OLIMEX/S3-OLinuXino/HARDWARE/S3-OLinuXino-Rev_A-preliminary/images/img3.png

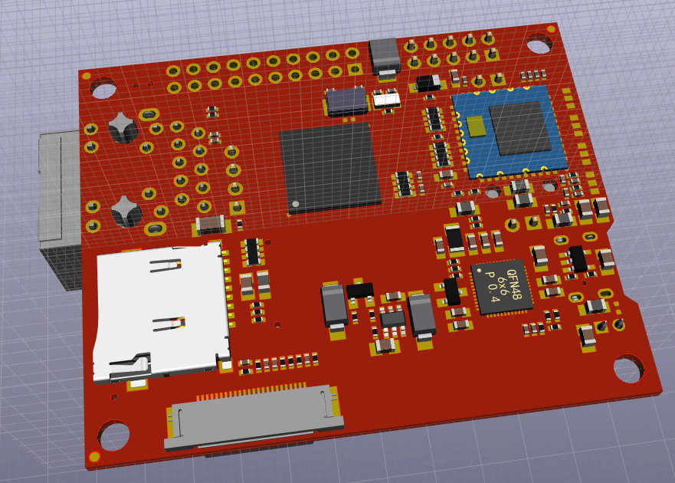
HARDWARE/S3-OLinuXino-Rev_A-preliminary/images/img3.png
