OLIMEX/S3-OLinuXino/HARDWARE/S3-OLinuXino-Rev_A-preliminary/3d/FPV-WZA21-40-LF_Molex-541044033.stp

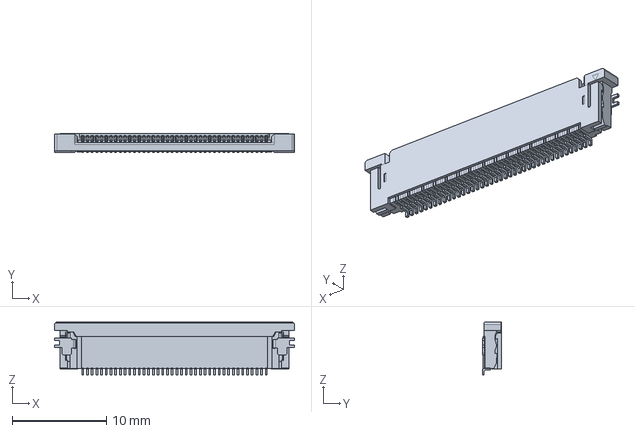
[picture p15: CAD file, 2020-04-24]
HARDWARE/S3-OLinuXino-Rev_A-preliminary/3d/FPV-WZA21-40-LF_Molex-541044033.stp
25.5 x 2.05 x 5.60 mm
