OLIMEX/S3-OLinuXino/HARDWARE/S3-OLinuXino_Rev_A-release/3d/SOT-23.step

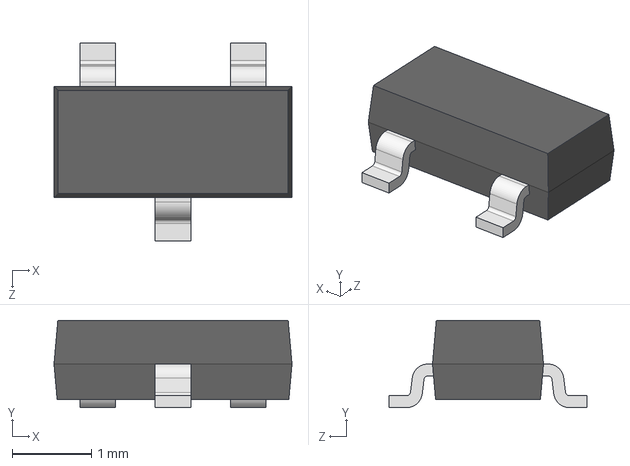
[picture p16: CAD file, 2020-04-24]
HARDWARE/S3-OLinuXino_Rev_A-release/3d/SOT-23.step
3.00 x 1.10 x 2.50 mm
