OLIMEX/S3-OLinuXino/HARDWARE/S3-OLinuXino-Rev_A-preliminary/3d/L-CD32_shielded.step

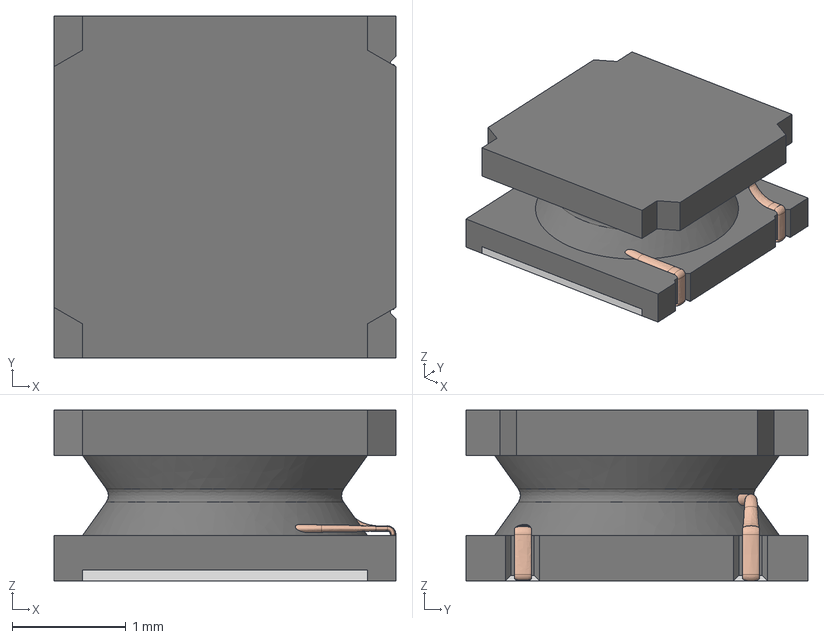
[picture p17: CAD file, 2020-04-24]
HARDWARE/S3-OLinuXino-Rev_A-preliminary/3d/L-CD32_shielded.step
3.00 x 3.00 x 1.50 mm
