OLIMEX/S3-OLinuXino/HARDWARE/S3-OLinuXino-Rev_A-preliminary/3d/TE_Connectivity-RJ45_JACK_MAG._POE_1GB_LED_1X1(2337992-8).stp

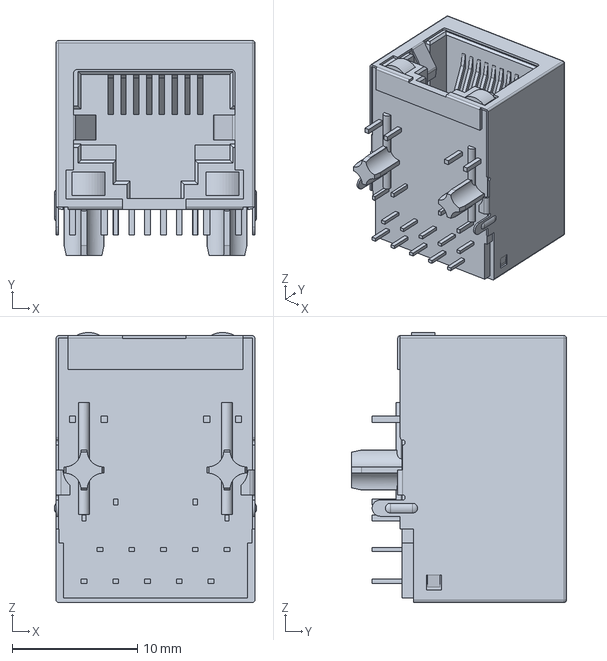
[picture p18: CAD file, 2020-04-24]
HARDWARE/S3-OLinuXino-Rev_A-preliminary/3d/TE_Connectivity-RJ45_JACK_MAG._POE_1GB_LED_1X1(2337992-8).stp
16.2 x 17.2 x 21.6 mm
