OLIMEX/S3-OLinuXino/HARDWARE/S3-OLinuXino_Rev_A-release/3d/it1185.step

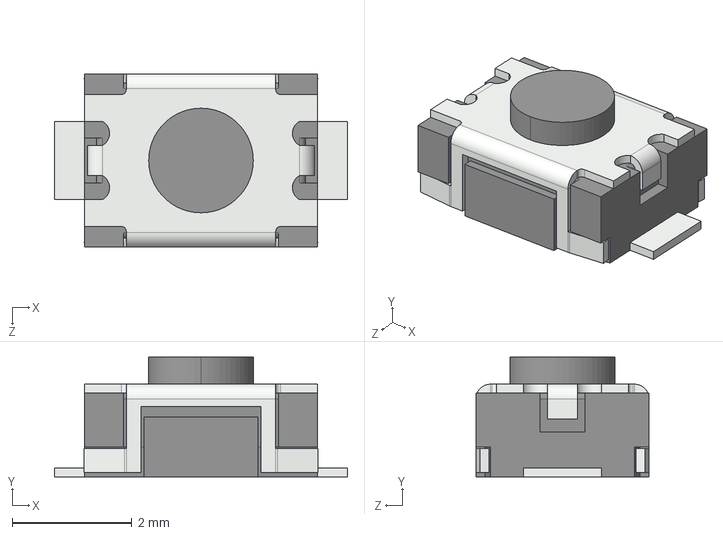
[picture p19: CAD file, 2020-04-24]
HARDWARE/S3-OLinuXino_Rev_A-release/3d/it1185.step
4.90 x 2.00 x 2.90 mm
