OLIMEX/S3-OLinuXino/HARDWARE/S3-OLinuXino_Rev_A-release/3d/RaspberryPiLCD-MiPi_Connector-TE_1-1734248-5.stp

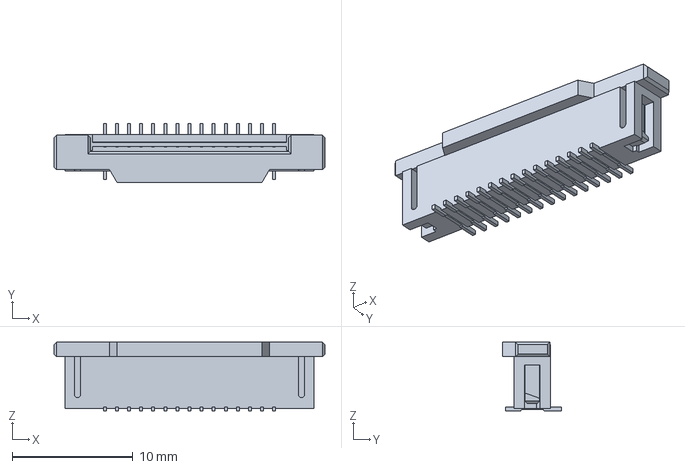
[picture p20: CAD file, 2020-04-24]
HARDWARE/S3-OLinuXino_Rev_A-release/3d/RaspberryPiLCD-MiPi_Connector-TE_1-1734248-5.stp
22.4 x 4.85 x 5.68 mm
