OLIMEX/S3-OLinuXino/HARDWARE/S3-OLinuXino-Rev_A-preliminary/3d/CUI_SJ-43515TS-SMT-TR.step

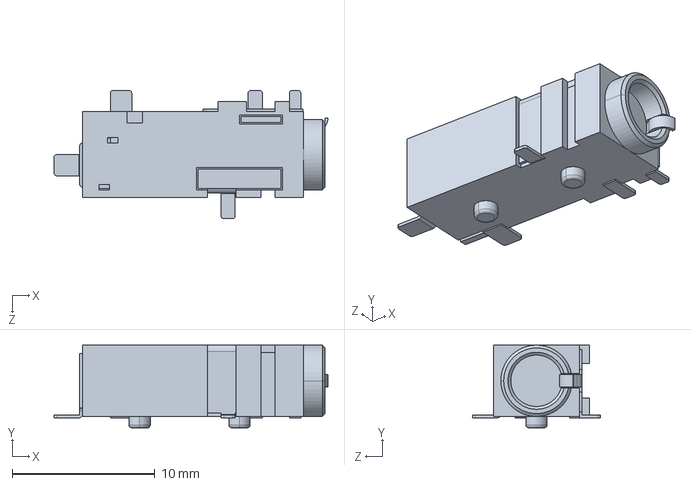
[picture p21: CAD file, 2020-04-24]
HARDWARE/S3-OLinuXino-Rev_A-preliminary/3d/CUI_SJ-43515TS-SMT-TR.step
19.2 x 5.80 x 9.00 mm
