OLIMEX/S3-OLinuXino/HARDWARE/S3-OLinuXino_Rev_A-release/3d/QSG5032.step

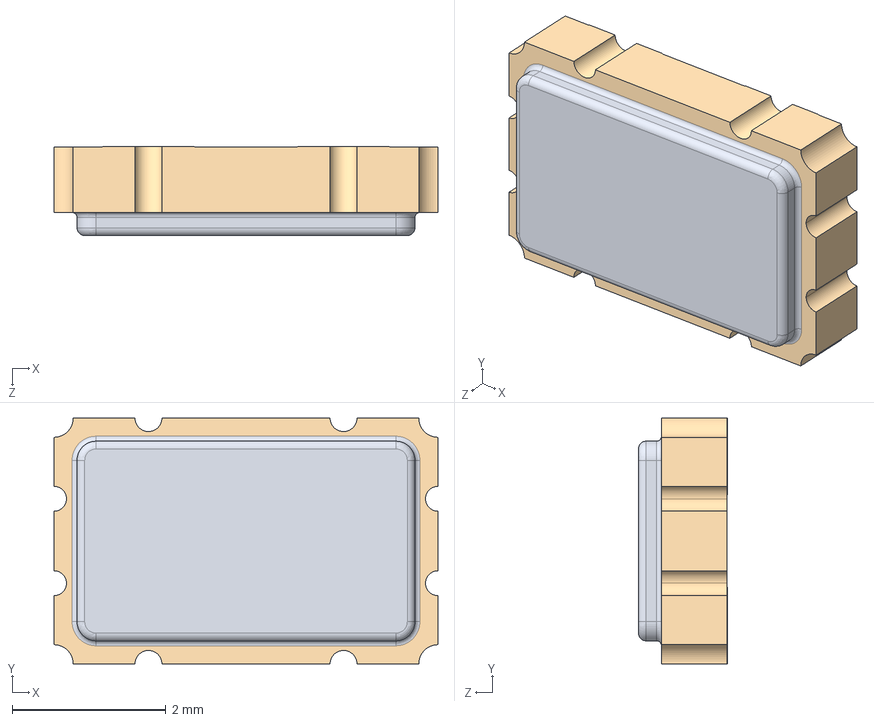
[picture p22: CAD file, 2020-04-24]
HARDWARE/S3-OLinuXino_Rev_A-release/3d/QSG5032.step
5.00 x 3.20 x 1.16 mm
