OLIMEX/S3-OLinuXino/HARDWARE/S3-OLinuXino-Rev_A-preliminary/3d/BGA-256_11.0x11.0mm_Layout20x20_P0.5mm_Ball0.3mm_Pad0.25mm_NSMD.step

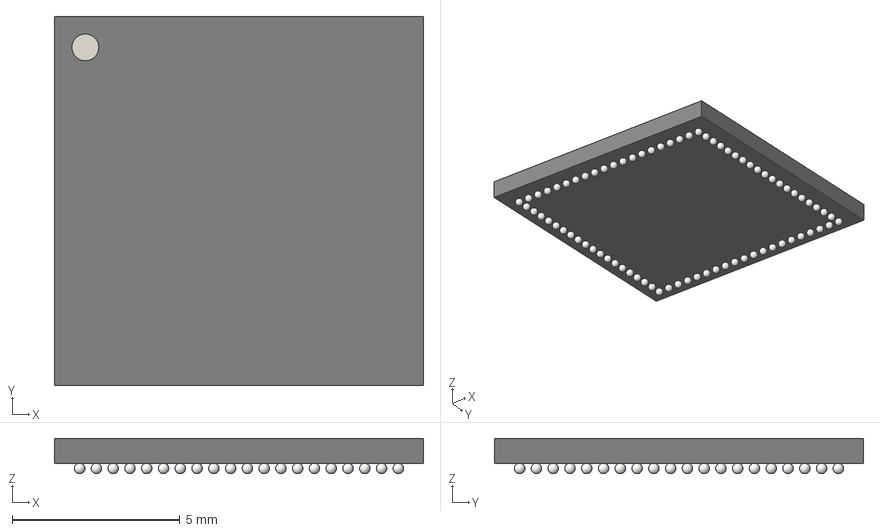
[picture p23: CAD file, 2020-04-24]
HARDWARE/S3-OLinuXino-Rev_A-preliminary/3d/BGA-256_11.0x11.0mm_Layout20x20_P0.5mm_Ball0.3mm_Pad0.25mm_NSMD.step
11.0 x 11.0 x 1.06 mm
