OLIMEX/S3-OLinuXino/HARDWARE/S3-OLinuXino_Rev_A-release/3d/SO-8_150mil---SN65HVDA1050AQDRQ1.STEP

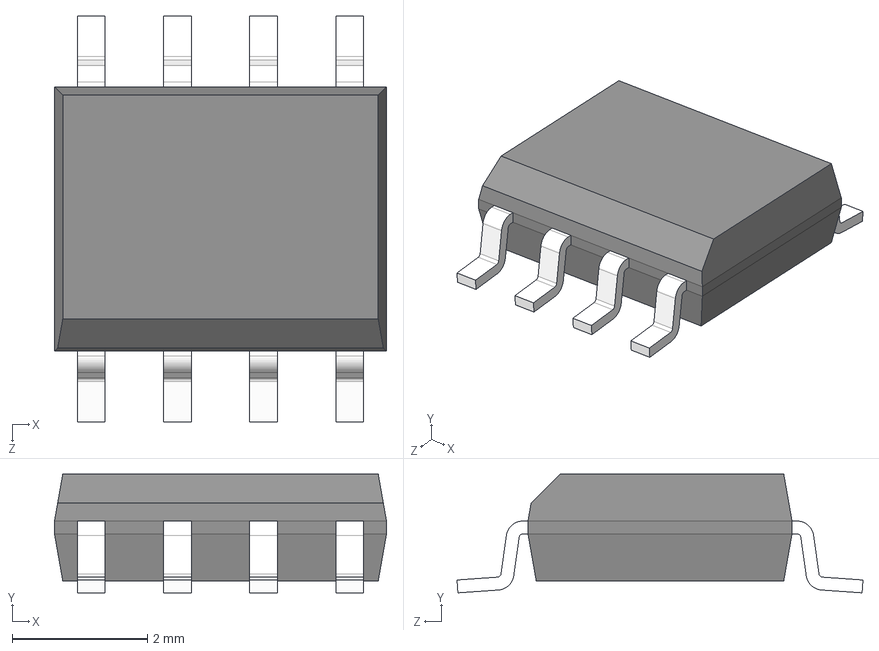
[picture p24: CAD file, 2020-04-24]
HARDWARE/S3-OLinuXino_Rev_A-release/3d/SO-8_150mil---SN65HVDA1050AQDRQ1.STEP
4.90 x 1.75 x 5.99 mm
