OLIMEX/S3-OLinuXino/HARDWARE/S3-OLinuXino-Rev_A-preliminary/3d/QFN-48_6x6mm_Pitch-0.4mm.STEP

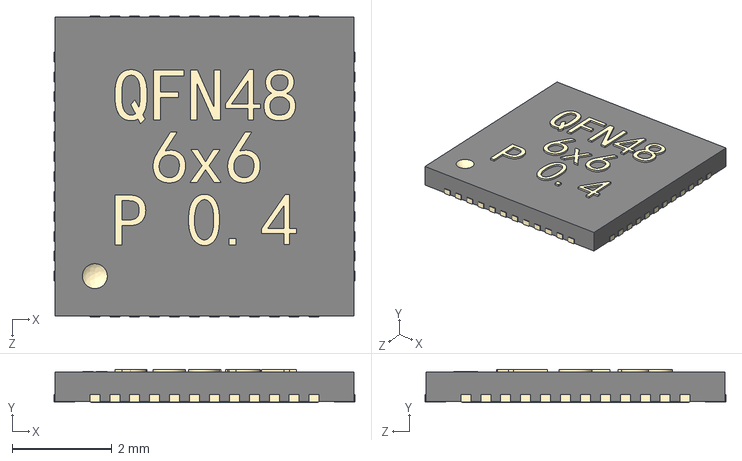
[picture p25: CAD file, 2020-04-24]
HARDWARE/S3-OLinuXino-Rev_A-preliminary/3d/QFN-48_6x6mm_Pitch-0.4mm.STEP
6.04 x 0.67 x 6.04 mm
