OLIMEX/S3-OLinuXino/HARDWARE/S3-OLinuXino_Rev_A-release/3d/L-CD75(YS75)_7.80x7.00x5.50mm.step

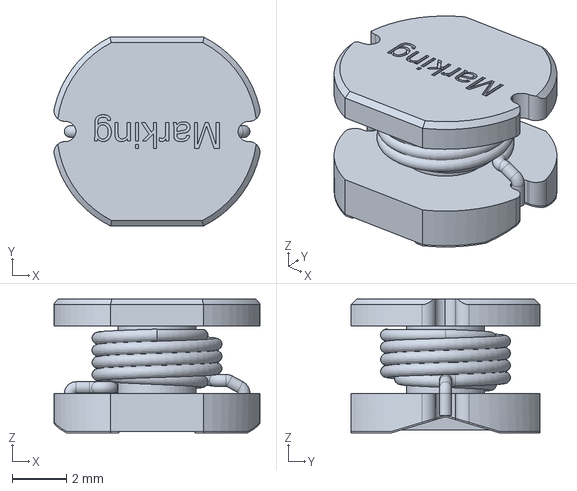
[picture p26: CAD file, 2020-04-24]
HARDWARE/S3-OLinuXino_Rev_A-release/3d/L-CD75(YS75)_7.80x7.00x5.50mm.step
7.63 x 7.00 x 4.95 mm
