OLIMEX/S3-OLinuXino/HARDWARE/S3-OLinuXino_Rev_A-release/3d/20PinMaleSmt.stp

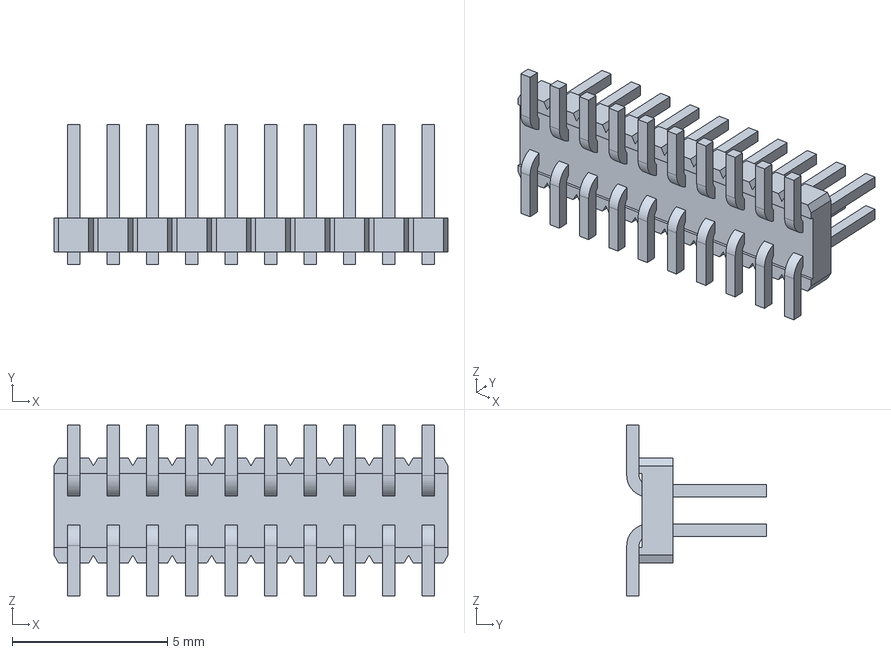
[picture p27: CAD file, 2020-04-24]
HARDWARE/S3-OLinuXino_Rev_A-release/3d/20PinMaleSmt.stp
12.7 x 4.50 x 5.50 mm
