OLIMEX/S3-OLinuXino/HARDWARE/S3-OLinuXino-Rev_A-preliminary/3d/SMD5032.STEP

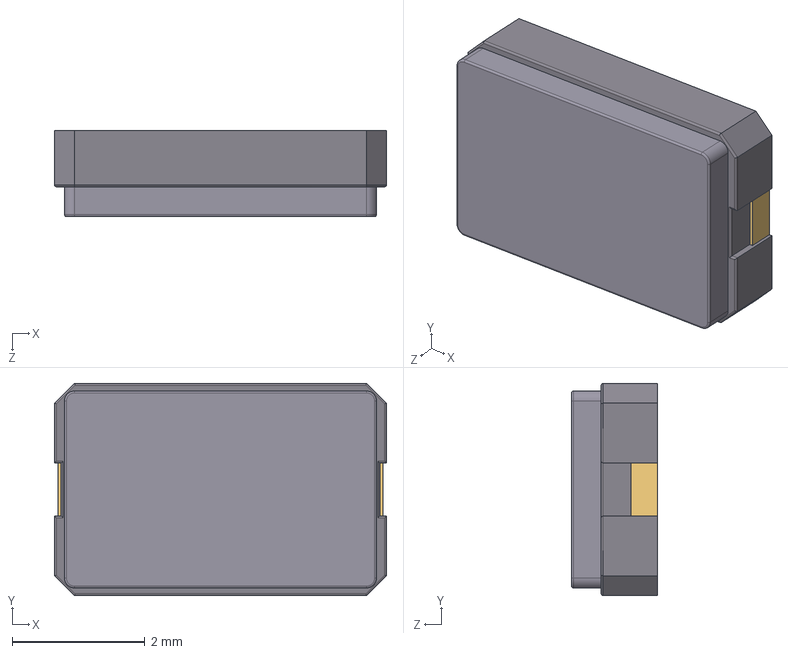
[picture p28: CAD file, 2020-04-24]
HARDWARE/S3-OLinuXino-Rev_A-preliminary/3d/SMD5032.STEP
5.00 x 3.20 x 1.30 mm
User Library-ABM3-1_Fillet002
User Library-ABM3-1_Fillet001
User Library-ABM3-1_Pad001
