OLIMEX/S3-OLinuXino/HARDWARE/S3-OLinuXino-Rev_A-preliminary/3d/HN1x2-PinHeader_1x02_P2.54mm_Vertical.step

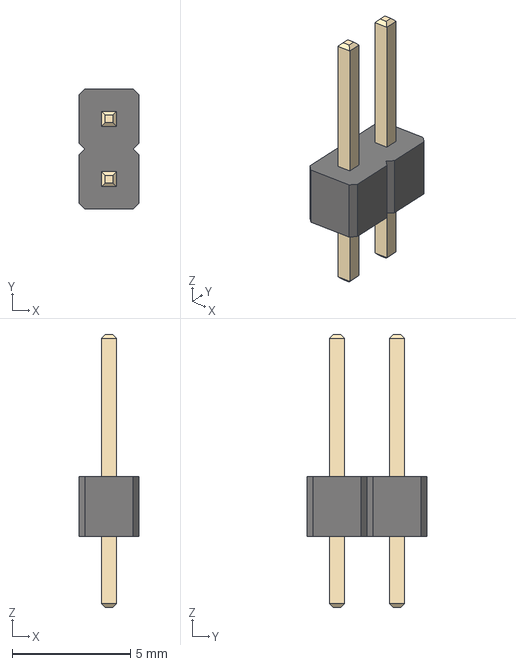
[picture p29: CAD file, 2019-10-25]
HARDWARE/S3-OLinuXino-Rev_A-preliminary/3d/HN1x2-PinHeader_1x02_P2.54mm_Vertical.step
2.54 x 5.08 x 11.5 mm
