OLIMEX/S3-OLinuXino/HARDWARE/S3-OLinuXino_Rev_A-release/3d/HN1x4-PinHeader_1x04_P2.54mm_Vertical.step

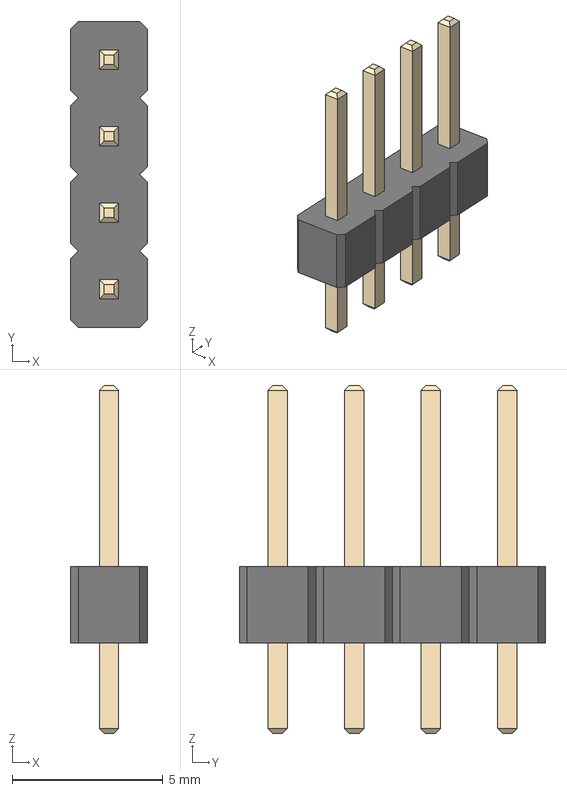
[picture p30: CAD file, 2019-10-25]
HARDWARE/S3-OLinuXino_Rev_A-release/3d/HN1x4-PinHeader_1x04_P2.54mm_Vertical.step
2.54 x 10.2 x 11.5 mm
