OLIMEX/S3-OLinuXino/HARDWARE/S3-OLinuXino-Rev_A-preliminary/3d/HN2x5-PinHeader_2x05_P2.54mm_Vertical.step

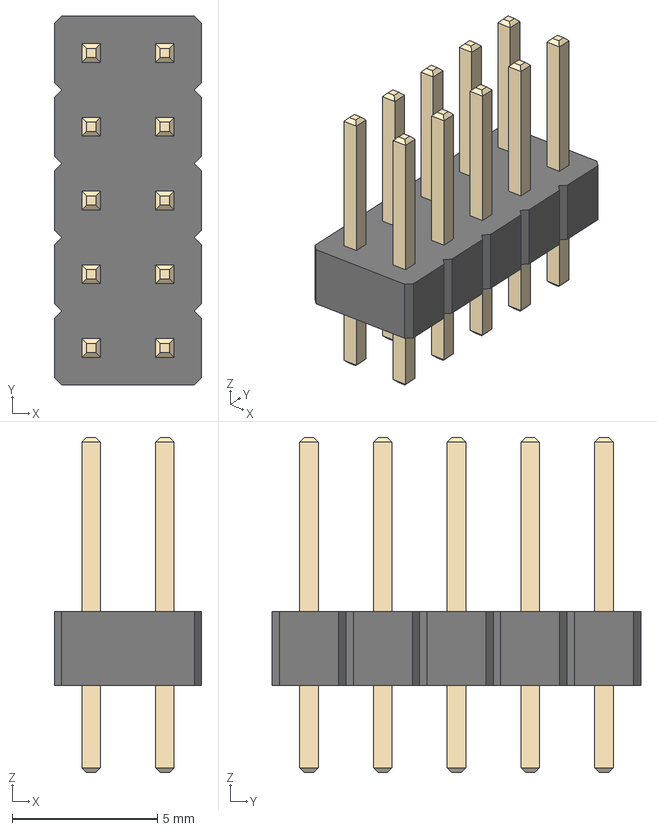
[picture p31: CAD file, 2019-10-25]
HARDWARE/S3-OLinuXino-Rev_A-preliminary/3d/HN2x5-PinHeader_2x05_P2.54mm_Vertical.step
5.08 x 12.7 x 11.5 mm
