OLIMEX/S3-OLinuXino/HARDWARE/S3-OLinuXino_Rev_A-release/3d/Molex_PicoBlade_530470210.step

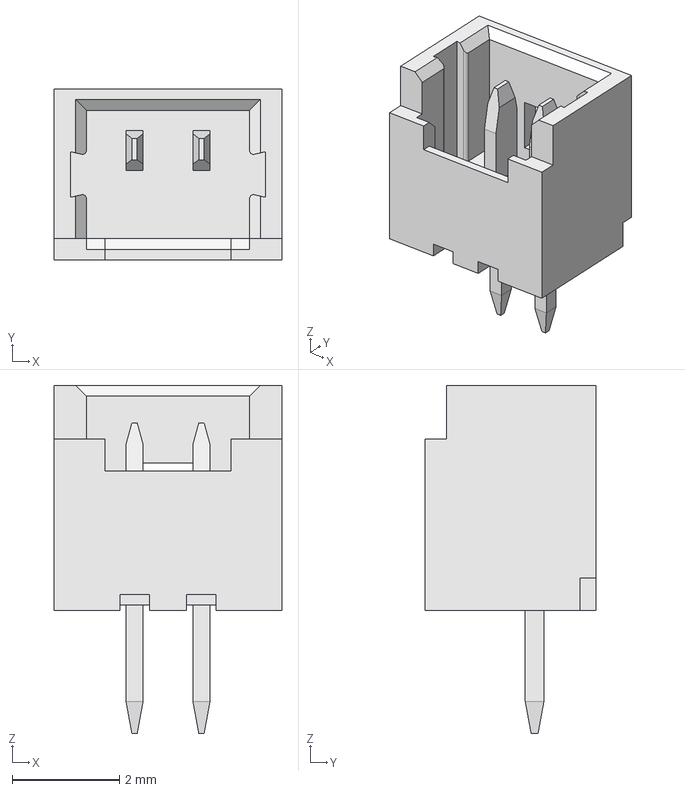
[picture p32: CAD file, 2019-10-25]
HARDWARE/S3-OLinuXino_Rev_A-release/3d/Molex_PicoBlade_530470210.step
4.25 x 3.20 x 6.50 mm
